diorcety/SS3/SIMS/ALIM.asc

B1: bv; V=0.8495*white(1e6*time)
C1: cap; 220µ; Rser=200m
C2: cap; 100n; Rser=0.03547
C3: cap; 56p
C4: cap; 47µ; Rser=3m
C5: cap; 1µ
C6: cap; 1µ
D1: diode; RB168VAM150
D2: diode; RBR2VWM40A
L1: ind; 15µ; Rser=77m
R1: res; 11
R2: res; 510k
R3: res; 20k
R4: res; 100k
R5: res; 510k
R6: res; 0.010
U1: TPS7A2033
U2: TPS54202
V1: voltage; SINE(0 16.97 50)
V2: voltage; 1V
Named nets: 0
.tran 200m
.include TPS54202.lib
.include TPS7A2033.lib
.options no_caret_warning
.options reltol=0.01
.options trtol=7
.options gmin=1e-12
.options plotwinsize=0
.meas TRAN P_IN AVG (V(n001)*I(D1)) FROM 20m TO 40m
.meas TRAN P_OUT AVG (V(n009)*I(R1)) FROM 20m TO 40m
