diorcety/SS3/SIMS/BBMOSFET.asc

B1: bv; V=white(1e6*time)*1.66
C1: cap; 4.7µ
D1: schottky; MBRS1100
D2: zener; PDZV12B
D3: TVSdiode; SMBJ36CA
L1: ind; 3µ; Rser=1m
M1: nmos; NTMFD5C672NL
M2: nmos; NTMFD5C672NL
R1: res; 866
R2: res; 3.5
R3: res; 100
R4: res; 4.7k
U1: PC817D
V2: voltage; PULSE(0 5 20m 1n 1n 20m 40m)
V3: voltage; 5V
V4: voltage; SINE(0 33.9 50)
Named nets: 0
.tran 0 100m 0 1u
.include NTMFD5C672NL.lib
.include SMCJ36CA.lib
