diorcety/SS3/SIMS/ZCD.asc

B1: bv; V=white(1e6*time)*1.66
D1: schottky; DI_BAT42WS
D2: schottky; DI_BAT42WS
R1: res; 4.7k
R2: res; 4.7k
R3: res; 1k
R4: res; 17.8k
R5: res; 1k
R6: res; 17.8k
U1: UniversalOpAmp
U2: UniversalOpAmp
V1: voltage; SINE(0 16.97 50)
V2: voltage; 2.5
V3: voltage; 3.3V
Named nets: 0
.tran 0 300m 0 1u
.MODEL DI_BAT42WS D  ( IS=87.5u RS=18.1m BV=30.0 IBV=500nC JO=8.88p  M=0.333 N=3.51 TT=7.20n )
