diorcety/SS3/SS3/heat.h

#ifndef HEAT_H_
#define HEAT_H_

#include <stdbool.h>

/*********************************************************************************************************************
 *                                                                                                                   *
 *                                                 CONSTANTS                                                         *
 *                                                                                                                   *
 *********************************************************************************************************************/

typedef enum {
  HEAT_STATE_NORMAL,
  HEAT_STATE_SETBACK,
  HEAT_STATE_STANDBY,
  HEAT_STATE_ERROR,
} HeatState;

/*********************************************************************************************************************
 *                                                                                                                   *
 *                                                   DATA                                                            *
 *                                                                                                                   *
 *********************************************************************************************************************/

extern HeatState heat_state;
extern int heat_setpoint;

/*********************************************************************************************************************
 *                                                                                                                   *
 *                                                 FUNCTIONS                                                         *
 *                                                                                                                   *
 *********************************************************************************************************************/

void heat_init(void);
void heat_toggle(void);
void heat_loop(void);
void heat_error(void);

#endif // HEAT_H_
