diorcety/SS3/SS3/st7789.h

#ifndef ST7789_H_
#define ST7789_H_

#if defined(USE_ST7789)

/*********************************************************************************************************************
 *                                                                                                                   *
 *                                                 FUNCTIONS                                                         *
 *                                                                                                                   *
 *********************************************************************************************************************/
void st7789_init(void);
void st7789_loop(void);

#endif

#endif // ST7789_H_
