diorcety/SS3/SS3/tick.h

#ifndef TICK_H_
#define TICK_H_

#include <stdbool.h>
#include <stdint.h>

/*********************************************************************************************************************
 *                                                                                                                   *
 *                                                  STRUCTS                                                          *
 *                                                                                                                   *
 *********************************************************************************************************************/

typedef struct timer {
  uint32_t start;
  uint32_t timeout;
  bool armed;
} tick_timer_t;

/*********************************************************************************************************************
 *                                                                                                                   *
 *                                                   DATA                                                            *
 *                                                                                                                   *
 *********************************************************************************************************************/

extern volatile uint32_t systick_counter;

/*********************************************************************************************************************
 *                                                                                                                   *
 *                                                 FUNCTIONS                                                         *
 *                                                                                                                   *
 *********************************************************************************************************************/

static inline void systick_inc(void) { systick_counter++; }

static inline uint32_t systick_get(void) { return systick_counter; }

static inline bool systick_elapsed(uint32_t start, uint32_t timeout) { return (systick_counter - start) >= timeout; }

void tick_timer_init(volatile tick_timer_t *t);
void tick_timer_start(volatile tick_timer_t *t, uint32_t timeout, bool restart);
uint32_t tick_timer_stop(volatile tick_timer_t *t);
bool tick_timer_elapsed(volatile tick_timer_t *t);
bool tick_timer_is_running(volatile tick_timer_t *t, bool update);

#endif // UTILS_H_
