diorcety/SS3/SS3/acquisition.h

#ifndef ACQUISITION_H_
#define ACQUISITION_H_

#include <stdbool.h>

/*********************************************************************************************************************
 *                                                                                                                   *
 *                                                   DATA                                                            *
 *                                                                                                                   *
 *********************************************************************************************************************/

extern float tc_right_temperature;
extern float tc_left_temperature;
extern float tc_right_voltage;
extern float tc_left_voltage;
extern int right_temperature;
extern int left_temperature;
extern int reed_value;
extern float kty_value;
extern int kty_temperature;

extern bool new_acquisition;

/*********************************************************************************************************************
 *                                                                                                                   *
 *                                                 FUNCTIONS                                                         *
 *                                                                                                                   *
 *********************************************************************************************************************/
void acquisition_init(void);
bool acquisition_trigger(void);
void acquisition_loop(void);

#endif // ACQUISITION_H_
