diorcety/SS3/SS3/button.h

#ifndef BUTTONS_H_
#define BUTTONS_H_

/*********************************************************************************************************************
 *                                                                                                                   *
 *                                                 CONSTANTS                                                         *
 *                                                                                                                   *
 *********************************************************************************************************************/

typedef enum {
  EVENT_NONE,
  EVENT_LEFT,
  EVENT_RIGHT,
  EVENT_PRESS,
  EVENT_LONG_PRESS,
} Event;

/*********************************************************************************************************************
 *                                                                                                                   *
 *                                                 FUNCTIONS                                                         *
 *                                                                                                                   *
 *********************************************************************************************************************/

void button_init(void);
void button_loop(void);
Event button_get_event(void);

#endif // BUTTONS_H_
