diorcety/SS3/SS3/iron.h

#ifndef IRON_H_
#define IRON_H_

#include <stdbool.h>

/*********************************************************************************************************************
 *                                                                                                                   *
 *                                                   DATA                                                            *
 *                                                                                                                   *
 *********************************************************************************************************************/
extern bool right_heat;
extern bool left_heat;
extern int right_duty;
extern int left_duty;

/*********************************************************************************************************************
 *                                                                                                                   *
 *                                                 FUNCTIONS                                                         *
 *                                                                                                                   *
 *********************************************************************************************************************/

void iron_init(void);
void iron_loop(void);
void iron_trigger(void);
bool iron_is_standby(void);

#endif // IRON_H_
