diorcety/SS3/SS3/seg7.h

#ifndef SEG7_H_
#define SEG7_H_

#if defined(USE_SEG7)

/*********************************************************************************************************************
 *                                                                                                                   *
 *                                                 FUNCTIONS                                                         *
 *                                                                                                                   *
 *********************************************************************************************************************/

void seg7_init(void);
void seg7_loop(void);

#endif

#endif // SEG7_H_
