diorcety/SS3/SS3/zcd.h

#ifndef ZCD_H_
#define ZCD_H_

/*********************************************************************************************************************
 *                                                                                                                   *
 *                                                   DATA                                                            *
 *                                                                                                                   *
 *********************************************************************************************************************/

extern int main_period;

/*********************************************************************************************************************
 *                                                                                                                   *
 *                                                 FUNCTIONS                                                         *
 *                                                                                                                   *
 *********************************************************************************************************************/

void zcd_init(void);
void zcd_loop(void);

#endif // ZCD_H_
