diorcety/SS3/SS3/calibration.h

#ifndef CALIBRATION_H_
#define CALIBRATION_H_

#include "interpolate2d.h"

/*********************************************************************************************************************
 *                                                                                                                   *
 *                                                  STRUCTS                                                          *
 *                                                                                                                   *
 *********************************************************************************************************************/

DEFINE_INTERPOLATE2D_TABLE(interpolate2d_table_u16_f32_t, uint16_t, float);

/*********************************************************************************************************************
 *                                                                                                                   *
 *                                                   DATA                                                            *
 *                                                                                                                   *
 *********************************************************************************************************************/

extern const interpolate2d_table_u16_f32_t tc_inter_table;
extern const interpolate2d_table_u16_f32_t kty_inter_table;

/*********************************************************************************************************************
 *                                                                                                                   *
 *                                                 FUNCTIONS                                                         *
 *                                                                                                                   *
 *********************************************************************************************************************/

DECLARE_INTERPOLATE2D_FUNC(interpolate2d_u16_f32, interpolate2d_table_u16_f32_t, uint16_t, float);

#endif // CALIBRATION_H_
